ElektronikaDonBosco/RGB-Matrix/PROYECT/Software/programa_prueba_matriz_led_2x2_3_colores.ino

int E0=16;
int E1=17;
int E2=18;
int E3=19;
int E4=20;
#include "Tlc5940.h"
int channel1 = 0;
int channel2 = 1;
int channel3 = 2;
int channel4 = 3;
int channel5 = 4;
int channel6 = 5;
int i;
int green;
int red;
int blue;
int tempo;
void setup() {
pinMode(E0,OUTPUT);
pinMode(E1,OUTPUT);
pinMode(E2,OUTPUT);
pinMode(E3,OUTPUT);
pinMode(E4,OUTPUT);

tempo=167;
green=0;
red=1600;i
blue=800; 

digitalWrite (E0,HIGH);
digitalWrite (E1,HIGH);
digitalWrite (E2,HIGH);
digitalWrite (E3,HIGH);
digitalWrite (E4,HIGH);
Tlc.init();
Tlc.clear();
}

void loop() {
  // RED

Tlc.set(channel1, red);
Tlc.set(channel2, red);
Tlc.update();
digitalWrite (E0,LOW);
digitalWrite (E1,LOW);
digitalWrite (E2,LOW);
digitalWrite (E3,LOW);
digitalWrite (E4,LOW);
delayMicroseconds(tempo);
Tlc.clear();
Tlc.update();

Tlc.set(channel1, red);
Tlc.set(channel2, red);

digitalWrite (E0,HIGH);
digitalWrite (E1,LOW);
digitalWrite (E2,LOW);
digitalWrite (E3,LOW);
digitalWrite (E4,LOW);
Tlc.update();

delayMicroseconds(tempo);
Tlc.clear();
Tlc.update();

  // GREEN

Tlc.set(channel3, green);
Tlc.set(channel5, green);

digitalWrite (E0,LOW);
digitalWrite (E1,LOW);
digitalWrite (E2,LOW);
digitalWrite (E3,LOW);
digitalWrite (E4,LOW);
Tlc.update();

delayMicroseconds(tempo);
Tlc.clear();
Tlc.update();

Tlc.set(channel3, green);
Tlc.set(channel5, green);

digitalWrite (E0,HIGH);
digitalWrite (E1,LOW);
digitalWrite (E2,LOW);
digitalWrite (E3,LOW);
digitalWrite (E4,LOW);
Tlc.update();

delayMicroseconds(tempo);
Tlc.clear();
Tlc.update();


  // BLUE

Tlc.set(channel4, blue);
Tlc.set(channel6, blue);

digitalWrite (E0,LOW);
digitalWrite (E1,LOW);
digitalWrite (E2,LOW);
digitalWrite (E3,LOW);
digitalWrite (E4,LOW);
Tlc.update();

delayMicroseconds(tempo);
Tlc.clear();
Tlc.update();

Tlc.set(channel4, blue);
Tlc.set(channel6, blue);

digitalWrite (E0,HIGH);
digitalWrite (E1,LOW);
digitalWrite (E2,LOW);
digitalWrite (E3,LOW);
digitalWrite (E4,LOW);
Tlc.update();

delayMicroseconds(tempo);
Tlc.clear();
Tlc.update();


}
